Board-Folk/NeoGeoAES-3.5/images/neogeo_aes-3-5-back-300dpi_90p.jpg

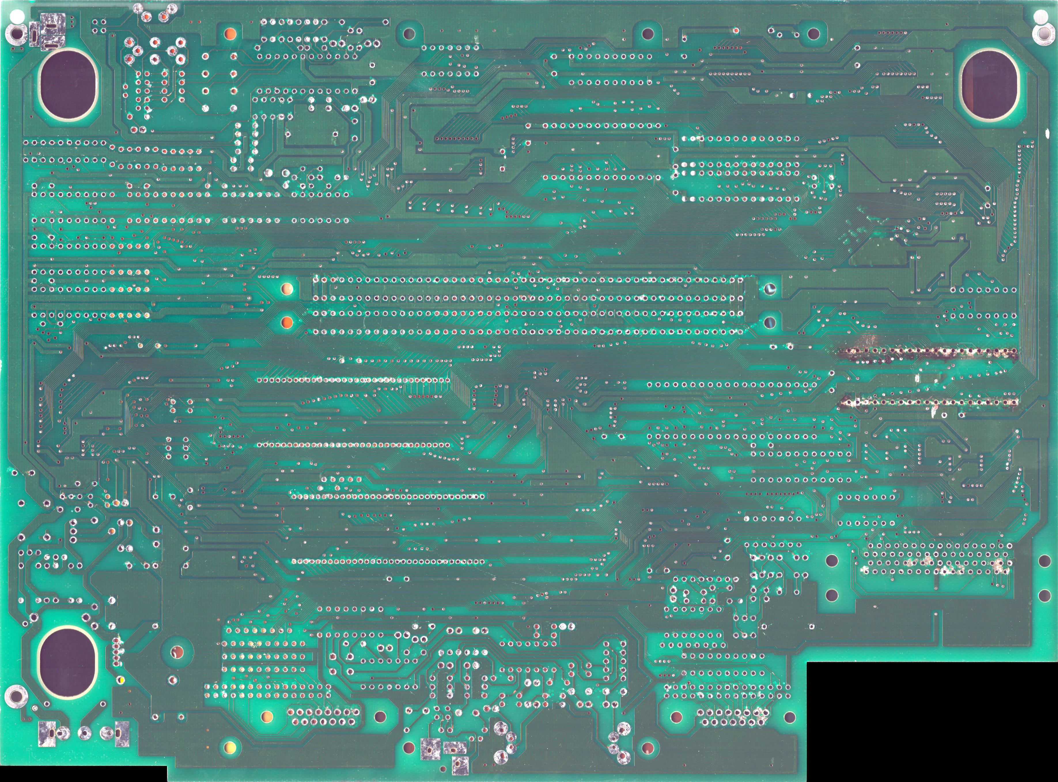
images/neogeo_aes-3-5-back-300dpi_90p.jpg
